Dmvkh/ClockBoxCounter/Sketch/Attiny/Serial.ino

const char TERMINATE_CHAR = '$';
const char CHECKSUM_CHAR = '%';
const char ATT_ID_CHAR = '@';
const char WMS_ID_CHAR = '&';

const char CHECKSUMM_ERR = '!';

void ReadSerial()
{
    portOne.listen();
    
    if (portOne.available() > 0)
    {        
        char command_id = portOne.read();        
        delay(10);
   
        if (command_id != WMS_ID_CHAR || !portOne.available())
        {
            return;
        }
        
        command_id = portOne.read();
        char commandData[255];
        char checksum = CHECKSUMM_ERR;
        
        byte dataLen = 0;

        bool termReceived = false;   
        delay(10);    
        
        while(portOne.available() > 0 && !termReceived)
        {
            delay(10);
            char cByte = portOne.read();
        
            if (cByte == TERMINATE_CHAR)
            {
                termReceived = true;
            }
            else if (cByte == CHECKSUM_CHAR)
            {         
                delay(10);
                if (portOne.available() > 0)
                {
                    checksum = portOne.read();
                }
            }
            else if (checksum == CHECKSUMM_ERR)
            {
                commandData[dataLen] = cByte;
                dataLen++;
            }
        }
        
        if (termReceived)
        {   
            // Release Wemos first     
            if (command_id != PING_ATTINY_SIG)
            {
                char msg[1] = { checksum };
                SendMessage_Serial(CHECKSUM_CONFIRM, 1, msg);
            }
            
            // Now Execute command
            ExecuteCommand(command_id, dataLen, commandData);
        }

        // Clear buffer leftover
        while (portOne.available() > 0) 
        {
           portOne.read();
           delay(10);
        }

        delay(10);
    }    
}

void SendMessage_Serial(char message_id, byte messageSize, char* msg)
{
    char serialOutput[messageSize + 4];
    serialOutput[0] = ATT_ID_CHAR;
    serialOutput[1] = message_id;
    
    for (byte i = 0; i < messageSize; ++i)
    {
        serialOutput[i + 2] = msg[i];
    }

    serialOutput[messageSize + 2] = TERMINATE_CHAR;
    serialOutput[messageSize + 3] = '\0';
    
    portOne.println(serialOutput);
}

void AnounceStartup()
{
    char msg[1] = { '1' };
    SendMessage_Serial(PING_ATTINY_SIG, 1, msg);
}

void ExecuteCommand(char command_id, byte dataLen, char* commandData)
{
    switch (command_id)
    {
        // Led ON/OFF control
        case SET_LEDS_MODE:
          
          if (dataLen == blink_modes_total)
          {
              for (byte i = 0; i < blink_modes_total; ++i)
              {
                  SetBlinkMode(i, commandData[i] == '1' ? 255 : 0, (char)('A' + 10), 255);
              }
          }
          
          break;

        // Blink control
        case SET_BLINK_MODE:

          if (dataLen == 8)
          {
              // Extract led no
              byte led_id = (byte)(commandData[0] - '0');
              byte blinkSpeed = ((byte)(commandData[1] - '0') * 100) + ((byte)(commandData[2] - '0') * 10) + ((byte)(commandData[3] - '0'));
              byte blink_limit = ((byte)(commandData[5] - '0') * 100) + ((byte)(commandData[6] - '0') * 10) + ((byte)(commandData[7] - '0'));
              
              SetBlinkMode(led_id, blinkSpeed, commandData[4], blink_limit);
          }

          break;

        case SET_BUZZER_PLAY:

          if (dataLen == 1)
          {
              switch (commandData[0])
              {
                  case '1': // Click
                    noTone();
                    tone(buzzer, 800, 5);
                    break;
              
                  case '2': // OK
                    noTone();
                    tone(buzzer, 1000, 200);
                    delay(220);
                    
                    noTone();    
                    tone(buzzer, 1500, 200);
                    break;
              
                  case '3': // Error
                    noTone();
                    tone(buzzer, 100, 200);
                    delay(220);
                    
                    noTone();    
                    tone(buzzer, 100, 200);
                    break;

                  case '4': // Alarm 1
                    
                    noTone();
                    tone(buzzer, 1000, 100);
                    tone(buzzer, 2000, 100);
                    tone(buzzer, 3000, 100);
                    break;

                  case '5': // Police alarm
                    
                    currentMelody = 1;
                    melodyNote = 0;
                    
                    break;
                  
                  case '6':  //Short buzz
                    noTone();
                    tone(buzzer, 3000, 10);
                    break;

                  case '7':  // Start Melody
                    noTone();
                    
                    currentMelody = 2;
                    melodyNote = 0;
                    
                    break;
              }
          }
          
          break;

        case PLAY_CUSTOM_TONE:
          
          if (dataLen == 8)
          {
              int playTone = (byte)(commandData[0] - '0') * 1000 + (byte)(commandData[1] - '0') * 100 + (byte)(commandData[2] - '0') * 10 + (byte)(commandData[3] - '0');
              int toneLen = (byte)(commandData[4] - '0') * 1000 + (byte)(commandData[5] - '0') * 100 + (byte)(commandData[6] - '0') * 10 + (byte)(commandData[7] - '0');
          
              noTone();
              tone(buzzer, playTone, toneLen);
          }
          
          break;

        case PING_ATTINY_SIG:

          // Wemos want to check if Attiny is on
          if (dataLen == 1)
          {
              AnounceStartup();
          }
          
          break;
    }
}
