Dmvkh/ClockBoxCounter/Sketch/Attiny/Buzz.ino

#define C0  16.35
#define Db0 17.32
#define D0  18.35
#define Eb0 19.45
#define E0  20.60
#define F0  21.83
#define Gb0 23.12
#define G0  24.50
#define Ab0 25.96
#define LA0 27.50
#define Bb0 29.14
#define B0  30.87
#define C1  32.70
#define Db1 34.65
#define D1  36.71
#define Eb1 38.89
#define E1  41.20
#define F1  43.65
#define Gb1 46.25
#define G1  49.00
#define Ab1 51.91
#define LA1 55.00
#define Bb1 58.27
#define B1  61.74
#define C2  65.41
#define Db2 69.30
#define D2  73.42
#define Eb2 77.78
#define E2  82.41
#define F2  87.31
#define Gb2 92.50
#define G2  98.00
#define Ab2 103.83
#define LA2 110.00
#define Bb2 116.54
#define B2  123.47
#define C3  130.81
#define Db3 138.59
#define D3  146.83
#define Eb3 155.56
#define E3  164.81
#define F3  174.61
#define Gb3 185.00
#define G3  196.00
#define Ab3 207.65
#define LA3 220.00
#define Bb3 233.08
#define B3  246.94
#define C4  261.63
#define Db4 277.18
#define D4  293.66
#define Eb4 311.13
#define E4  329.63
#define F4  349.23
#define Gb4 369.99
#define G4  392.00
#define Ab4 415.30
#define LA4 440.00
#define Bb4 466.16
#define B4  493.88
#define C5  523.25
#define Db5 554.37
#define D5  587.33
#define Eb5 622.25
#define E5  659.26
#define F5  698.46
#define Gb5 739.99
#define G5  783.99
#define Ab5 830.61
#define LA5 880.00
#define Bb5 932.33
#define B5  987.77
#define C6  1046.50
#define Db6 1108.73
#define D6  1174.66
#define Eb6 1244.51
#define E6  1318.51
#define F6  1396.91
#define Gb6 1479.98
#define G6  1567.98
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
                        break;

                    case 20:
                        tone(buzzer, C6, noteDelay);
                        break;
                    
                    case 21:
                        tone(buzzer, LA5, noteDelay);
                        break;

                    case 22:
                        tone(buzzer, B5, noteDelay);
                        break;

                    case 23:
                        tone(buzzer, C6, noteDelay);
                        break;

                    case 24:                    
                        tone(buzzer, D6, 400);
                        noteDelay = 600;
                        break;
                    
                    case 25:
                        noteDelay = 230;
                        tone(buzzer, D6, 220);
                        break;

                    case 26:
                        tone(buzzer, D6, 220);
                        break; 
                                                                                                                                              
                    case 27:
                        tone(buzzer, D6, 220);
                        break;  
                        
                    case 28:
                      noteDelay = 400;
                        tone(buzzer, D6, noteDelay);
                        break;
                                                
                    case 29:
                      currentMelody = 0;
                      break;
                }
                
                melodyNote++;
                                
              break;
        }

        playMillis = currentMillis;
    }
}
